lukasx999/ZeroEmission_Zeitnehmung/02_GUI/assets/frame0/image_1.png

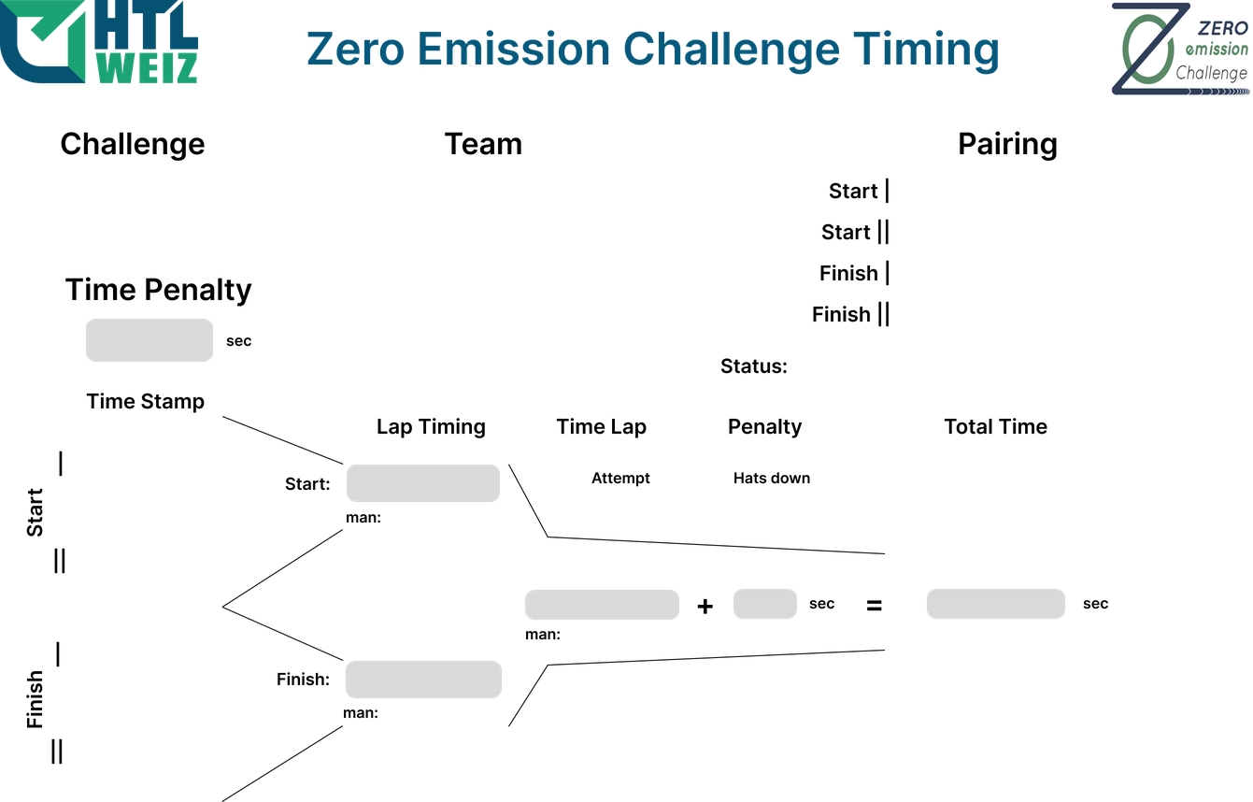
02_GUI/assets/frame0/image_1.png
